SchneHa/P1-WiFi-Gateway/debug.ino

/*
 * Copyright (c) 2022 Ronald Leenes
 *
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
 */

/**
 * @file debug.ino
 * @author Ronald Leenes
 * @date 28.12.2022
 *
 * @brief This file contains debug functions 
 *
 * @see http://esp8266thingies.nl
 */
 
void readVoltage() { // read internal VCC
  volts = ESP.getVcc();
  debugff("The internal VCC reads %1.2f volts\n", volts / 1000);
}

void PrintConfigData(){
  debugln();

  debug("dataSet : ");
    debugln(config_data.dataSet);
  debugln();

  debug("Admin password : ");
    debugln(config_data.adminPassword);
  debugln();

  debug("SSID : ");
    debugln(config_data.ssid);
  debug("password : ");
    debugln(config_data.password);
  debugln();

  debug("DomoticxIP : ");
    debugln(config_data.domoticzIP);
  debug("DomoticzPort : ");
    debugln(config_data.domoticzPort);
  debug("domotixzGasIdx : ");
   debugln(config_data.domoticzGasIdx);
  debug("domotixzEnergyIdx : ");
   debugln(config_data.domoticzEnergyIdx);
  debugln();

  debug("mqttIP : ");
    debugln(config_data.mqttIP);
  debug("mqttPort : ");
    debugln(config_data.mqttPort);
  debug("mqttUser : ");
    debugln(config_data.mqttUser);
  debug("mqttPass : ");
    debugln(config_data.mqttPass);
  debug("mqttTopic : ");
    debugln(config_data.mqttTopic);
  debugln();

  debug("cfosIP : ");
    debugln(config_data.cfosIP);
  debug("cfosPort : ");
    debugln(config_data.cfosPort);
  debug("cfosUsr : ");
    debugln(config_data.cfosUsr);
  debug("cfosPwd : ");
    debugln(config_data.cfosPwd);
  debug("cfosID : ");
    debugln(config_data.cfosID);
  debug("cfosModel : ");
    debugln(config_data.cfosModel);
  debugln();

//  debug("mqttGasIP : ");
//    debugln(config_data.mqttGasIP);
//  debug("mqttGasPort : ");
//    debugln(config_data.mqttGasPort);
//  debug("mqttGasUser : ");
//    debugln(config_data.mqttGasUser);
//  debug("mqttGasPass : ");
//    debugln(config_data.mqttGasPass);
  debug("mqttGasTopic : ");
    debugln(config_data.mqttGasTopic);
  debugln();
  debug("mqttGasTopicT : ");
    debugln(config_data.mqttGasTopicT);
  debugln();
//  debug("cfosVA : ");
//    debugln(config_data.cfosVA);
//  debug("cfosIsVA : ");
//    debugln(cfosIsVA);

  debug("interval : ");
    debugln(config_data.interval);
  debug("json : ");
    debugln(config_data.domo);
  debug("mqtt : ");
    debugln(config_data.mqtt);
  debug("cfos : ");
    debugln(config_data.cfos); 
  debug("mgas : ");
    debugln(config_data.mgas);  
  debug("watt : ");
    debugln(config_data.watt);
  debug("telnet : ");
    debugln(config_data.telnet);
  debugln();
}
