SchneHa/P1-WiFi-Gateway/JSON.ino

/*
 * Copyright (c) 2022 Ronald Leenes
 *
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
 */

/**
 * @file JSON.ino
 * @author Ronald Leenes
 *         Hans Schneider
 * @date 28.12.2022
 *       03.03.2023
 *
 * @brief This file contains the JSON functions for communicating with Domoticz and cFos Power Brain Wallbox
 *
 * @see http://esp8266thingies.nl
 */
 
void doJSON() {
  UpdateElectricity();
  UpdateGas();
}

bool DomoticzJson(char* idx, int nValue, char* sValue){
  WiFiClient client;
  HTTPClient http;
  bool retVal = false;
  char url[255];
 
  if (config_data.domoticzIP[0] != '-') {
    sprintf(url, "http://%s:%s/json.htm?type=command&param=udevice&idx=%s&nvalue=%d&svalue=%s", config_data.domoticzIP, config_data.domoticzPort, idx, nValue, sValue);

    debugff("[HTTP] GET... URL: %s\n",url);
    http.begin(client, url); //HTTP
    int httpCode = http.GET();
    // httpCode will be negative on error
    if (httpCode > 0) { // HTTP header has been sent and Server response header has been handled
      debugff("[HTTP] GET... code: %d\n", httpCode);
      // file found at server
      if (httpCode == HTTP_CODE_OK) {
        String payload = http.getString();
        retVal = true;
        entitledToSleep = true;
      }
    } else {
      debugff("[HTTP] GET... failed, error: %s\n", http.errorToString(httpCode).c_str());
      }
    http.end();
    return retVal;
  } // we just return if there is no IP to report to.
  return true;
}

void UpdateGas(){  //sends over the gas setting to server(s)
  if(strncmp(gasReceived5min, prevGAS, sizeof(gasReceived5min)) != 0){          // if we have a new value, report
    DomoticzJson(config_data.domoticzGasIdx, 0, gasDomoticz);// gasReceived5min);
    debug("Gas: ");
    debugln(gasDomoticz);
    strcpy(prevGAS, gasReceived5min);                              // retain current value for future reference
  }
}

void UpdateElectricity(){
  char sValue[255];
  //  sprintf(sValue, "%d.3;%d.3;%d.3;%d.3;%d;%d", electricityUsedTariff1, electricityUsedTariff2, mEOLT, mEOHT, mEAV, mEAT);
  sprintf(sValue, "%s;%s;%s;%s;%s;%s", electricityUsedTariff1, electricityUsedTariff2, electricityReturnedTariff1, electricityReturnedTariff2, actualElectricityPowerDelivered, actualElectricityPowerReturned);
  debugln(sValue);
  DomoticzJson(config_data.domoticzEnergyIdx, 0, sValue);
}

void doCFOS() {
  if (config_data.cfos[0] = 'j') {
    WiFiClient client;
    HTTPClient http;
    char url[255];

// Workaround for SmartMeter T211 in Belgium
    if (!reportInDecimals) {  // Anzeige in kW
      dtostrf(atof(electricityUsedTariff1)+atof(electricityUsedTariff2), 1, 2, cumulativeActiveImport);
      dtostrf(atof(electricityReturnedTariff1)+atof(electricityReturnedTariff2), 1, 2, cumulativeActiveExport);
      dtostrf(atof(instantaneousCurrentL1)*10, 1, 2, CurrentL1);
      dtostrf(atof(instantaneousCurrentL2)*10, 1, 2, CurrentL2);
      dtostrf(atof(instantaneousCurrentL3)*10, 1, 2, CurrentL3);
      }
    else {  // Anzeige in W
      dtostrf((atof(electricityUsedTariff1)+atof(electricityUsedTariff2))*1000, 1, 2, cumulativeActiveImport);
      dtostrf((atof(electricityReturnedTariff1)+atof(electricityReturnedTariff2))*1000, 1, 2, cumulativeActiveExport);
      dtostrf((atof(actualElectricityPowerDelivered)-atof(actualElectricityPowerReturned))*(1000), 1, 2, actualPowerImportExport);
      dtostrf(atof(instantaneousCurrentL1)*1000, 1, 2, CurrentL1);
      dtostrf(atof(instantaneousCurrentL2)*1000, 1, 2, CurrentL2);
      dtostrf(atof(instantaneousCurrentL3)*1000, 1, 2, CurrentL3);
    }
// end Workaround
    
    sprintf(url, "http://%s:%s@%s:%s/cnf?cmd=set_ajax_meter&dev_id=%s&model=%s&import_wh=%s&export_wh=%s&voltage=%s,%s,%s&current=%s,%s,%s&power_w=%s", config_data.cfosUsr, config_data.cfosPwd, config_data.cfosIP, config_data.cfosPort, config_data.cfosID, config_data.cfosModel, cumulativeActiveImport, cumulativeActiveExport, instantaneousVoltageL1, instantaneousVoltageL2, instantaneousVoltageL3, CurrentL1, CurrentL2, CurrentL3, actualPowerImportExport); // positiv: Netzbezug, negativ: Einspeisung
    debugff("[HTTP] GET... URL: %s\n",url);
    http.begin(client, url); //HTTP
    int httpCode = http.GET();
    // httpCode will be negative on error
    if (httpCode > 0) { // HTTP header has been sent and Server response header has been handled
      debugff("[HTTP] GET... code: %d\n", httpCode);
      // file found at server
      if (httpCode == HTTP_CODE_OK) {
         String payload = http.getString();
         entitledToSleep = true;
         }
      } else {
        debugff("[HTTP] GET... failed, error: %s\n", http.errorToString(httpCode).c_str());
      }
    http.end();
  } // we just return if there is no IP to report to.
}
